tmarhguy/cpu/schematics/ltspice/models/README.md

# SPICE Models

This directory contains SPICE transistor models and libraries used for circuit simulation.

## Model Files

- `mosfet_models.lib` - MOSFET model library

## Usage

Include model files in your SPICE netlists using `.lib` directives:

```
.lib mosfet_models.lib
```
