tmarhguy/cpu/media/design/electric/design_electric_and.png

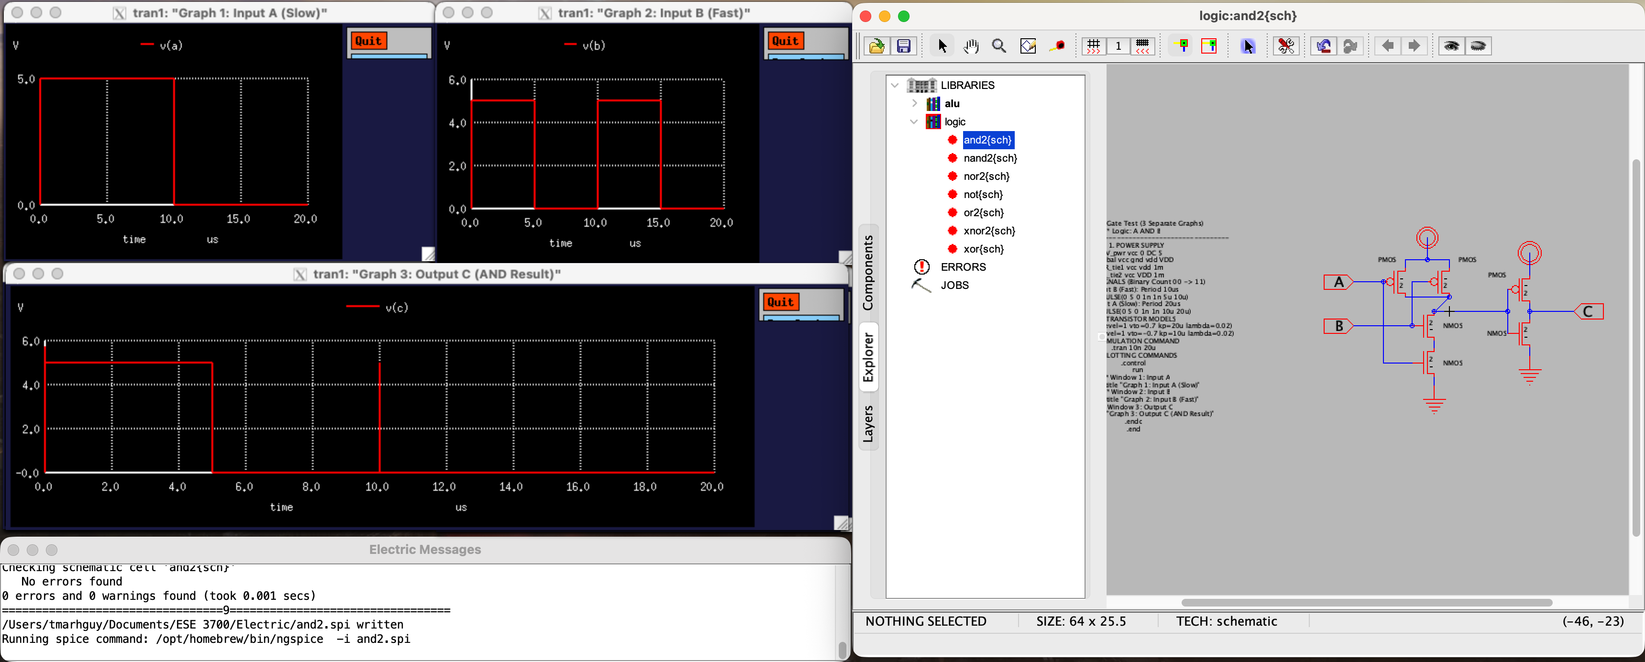
media/design/electric/design_electric_and.png
