tmarhguy/cpu/media/design/electric/design_electric_or.png

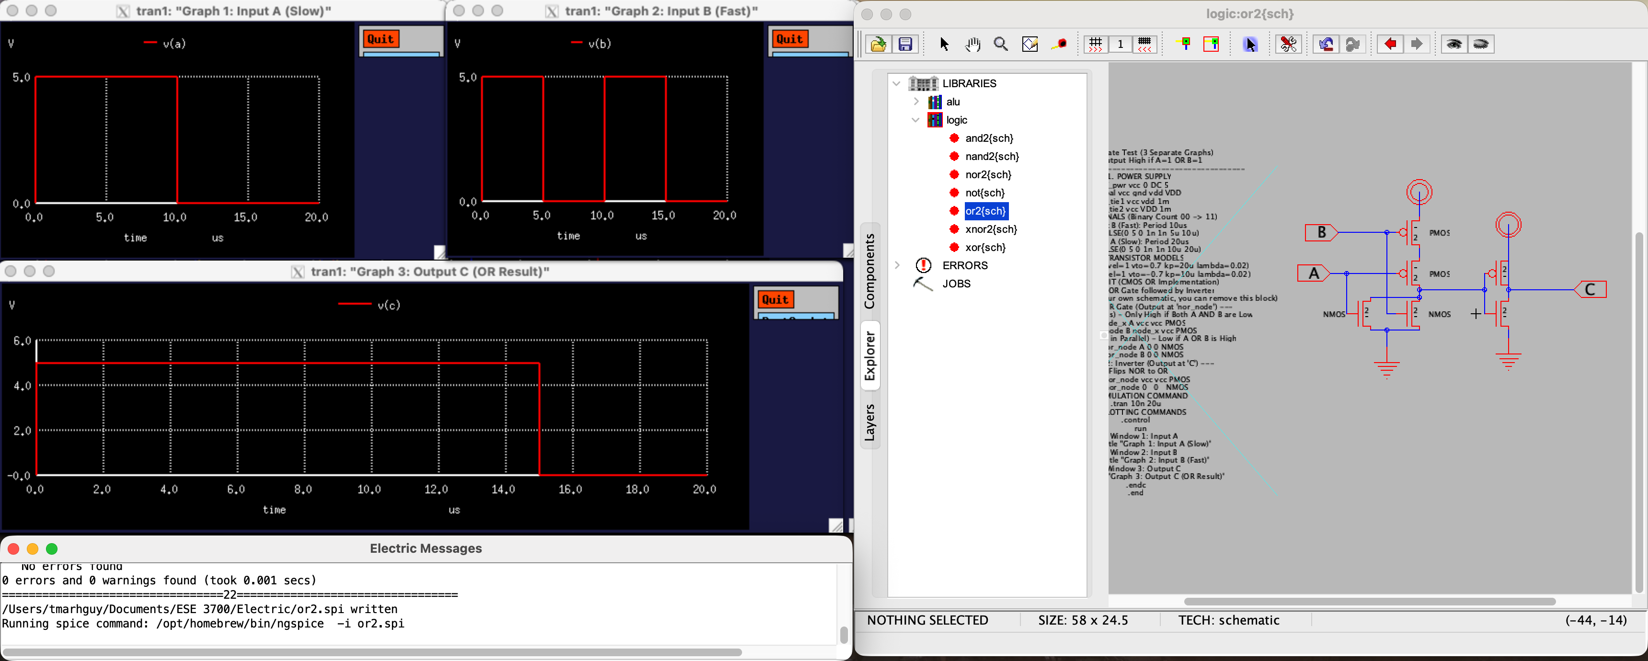
media/design/electric/design_electric_or.png
