tmarhguy/cpu/media/design/electric/design_electric_xnor.png

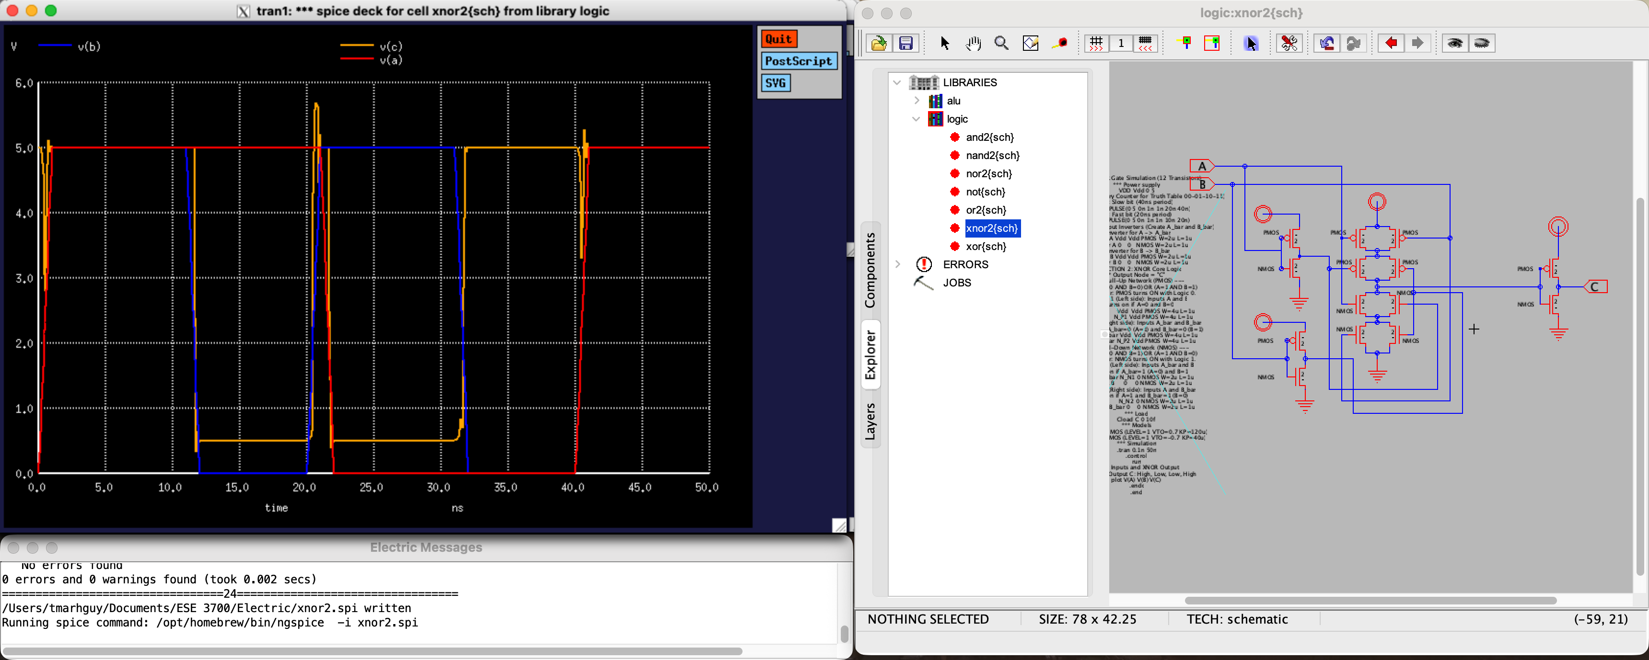
media/design/electric/design_electric_xnor.png
