tmarhguy/cpu/media/design/kicad/design_kicad_control_schematic.jpg

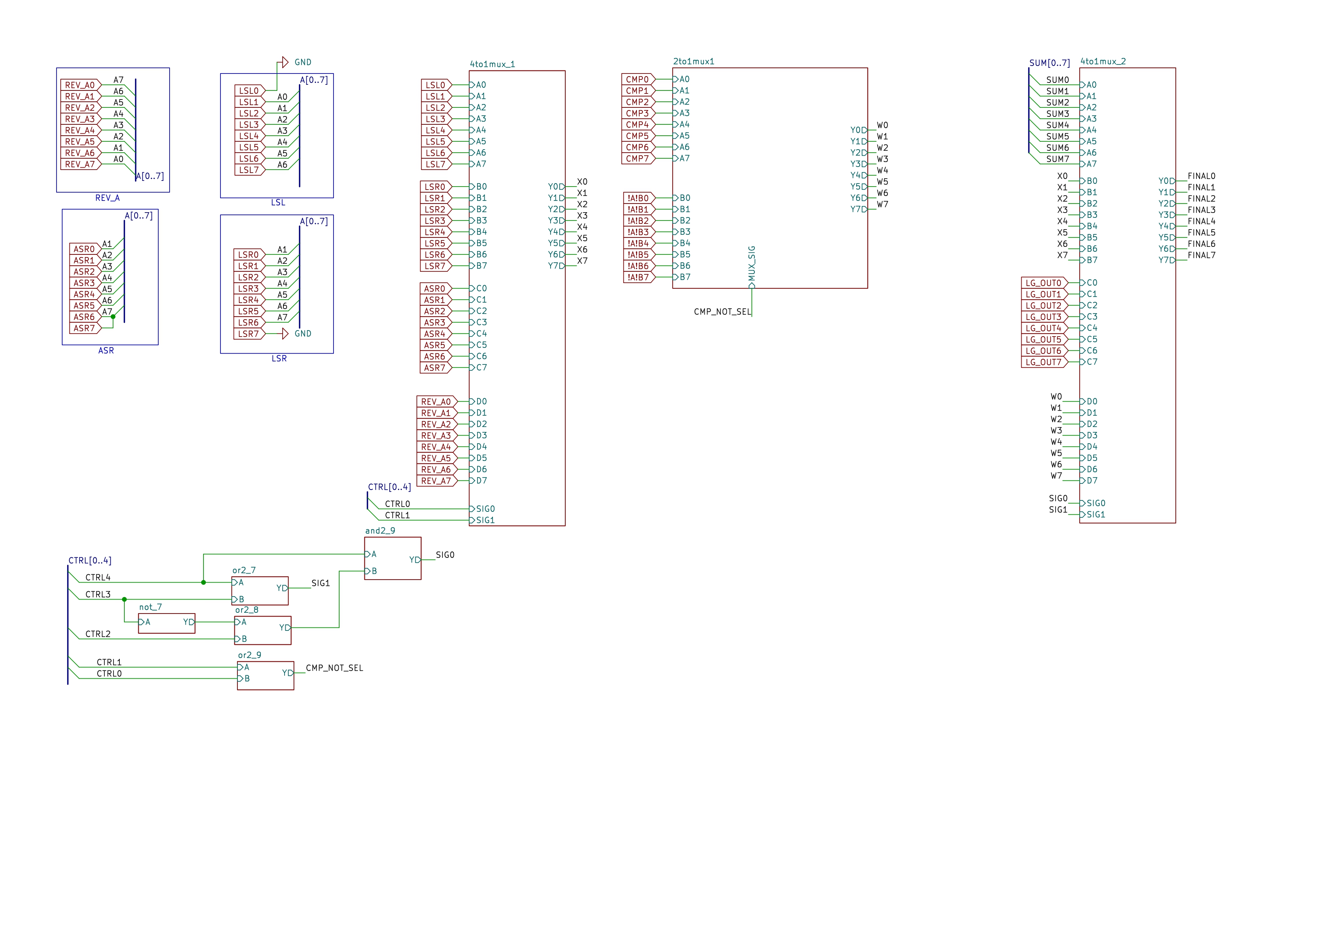
media/design/kicad/design_kicad_control_schematic.jpg
