tmarhguy/cpu/media/design/kicad/design_kicad_flags_schematic.jpg

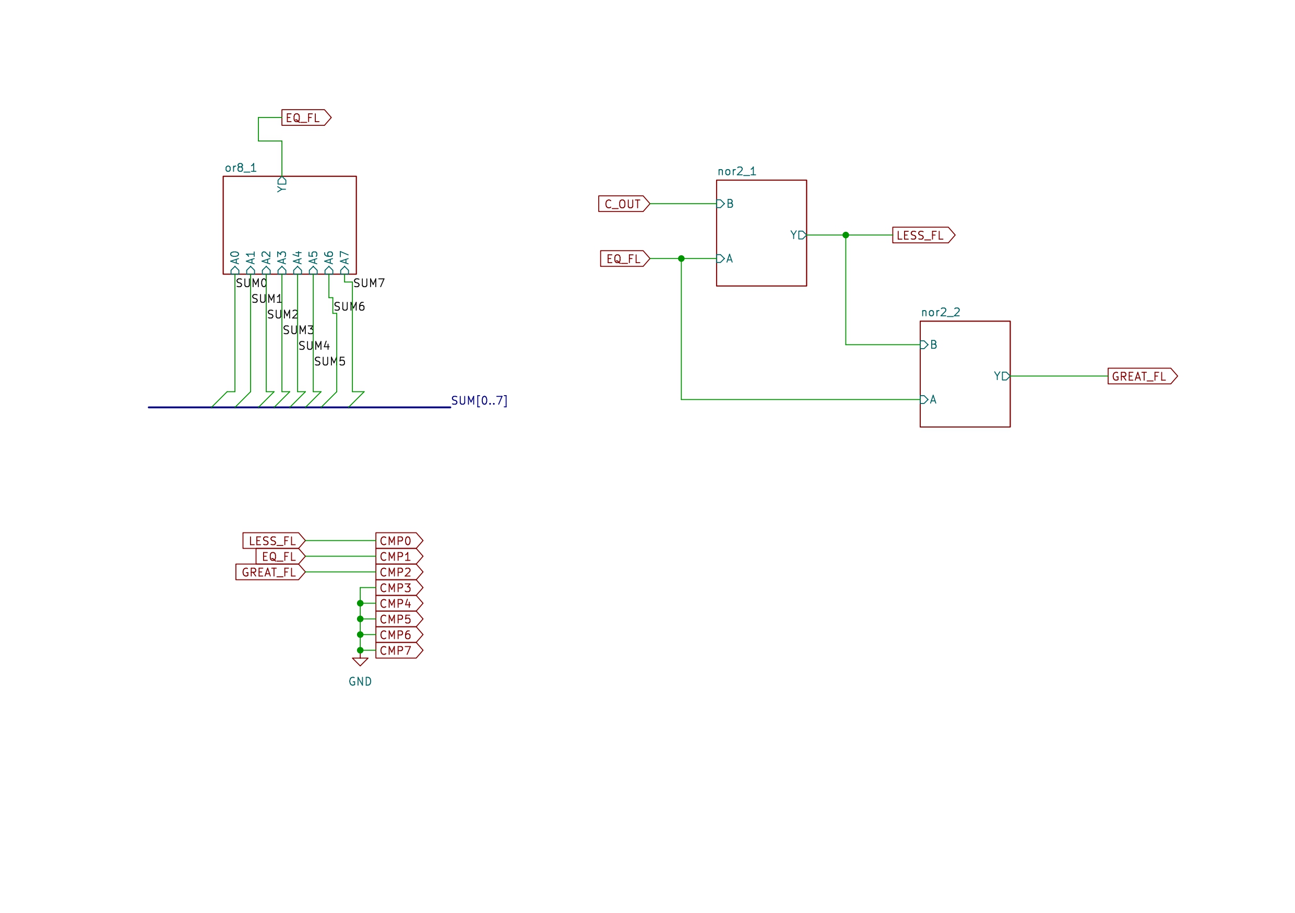
media/design/kicad/design_kicad_flags_schematic.jpg
