tmarhguy/cpu/media/gates/and/and.png

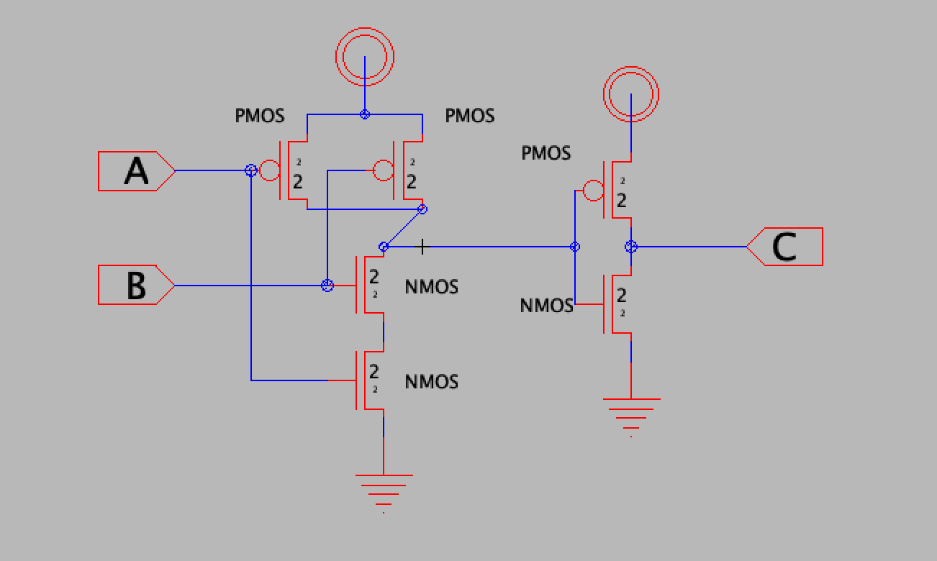
media/gates/and/and.png
