tmarhguy/cpu/media/gates/nand/nand.png

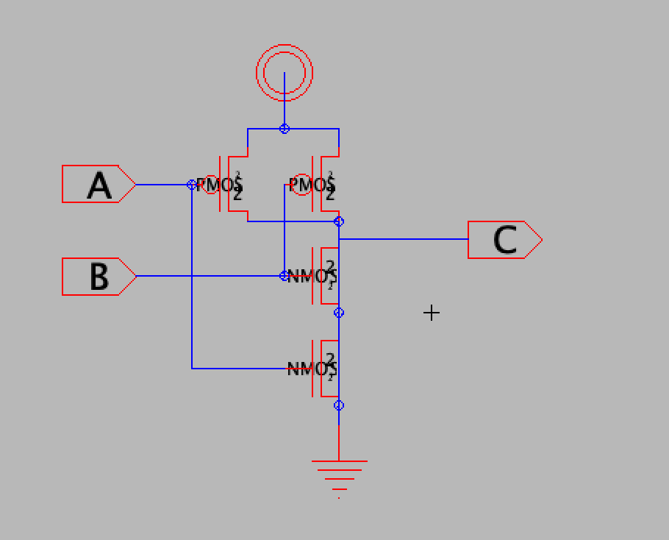
media/gates/nand/nand.png
