tmarhguy/cpu/media/gates/nor/nor.png

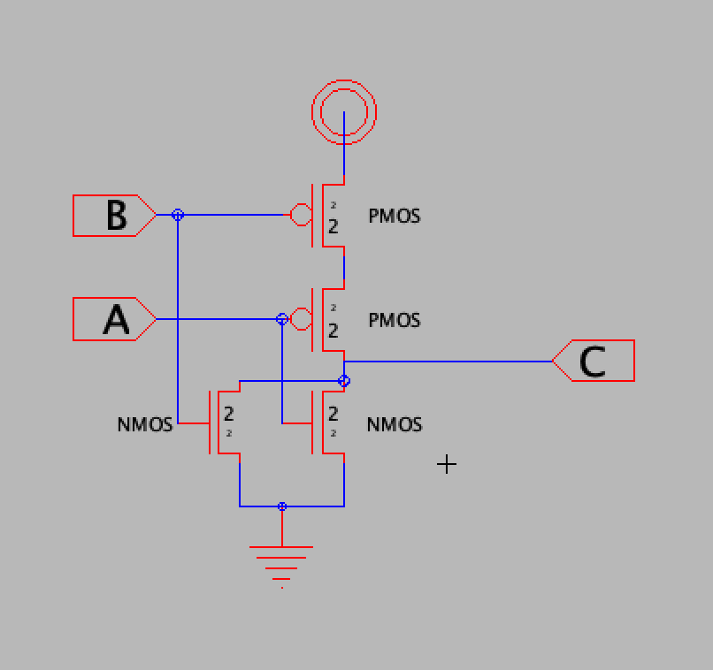
media/gates/nor/nor.png
