tmarhguy/cpu/media/gates/not/not-pcb view.png

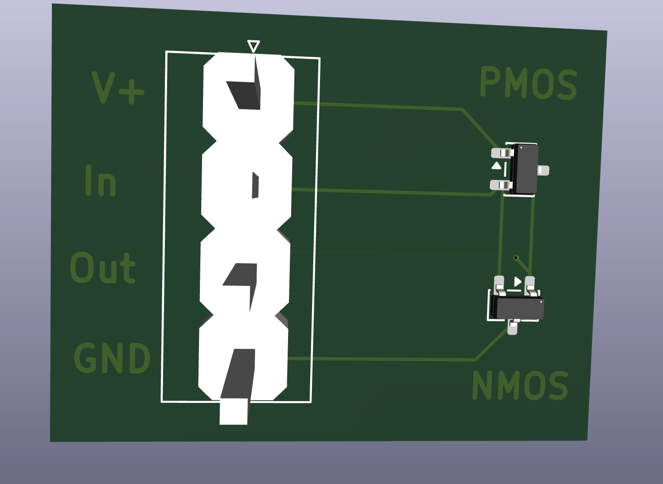
media/gates/not/not-pcb view.png
