tmarhguy/cpu/media/gates/not/not-schematics.png

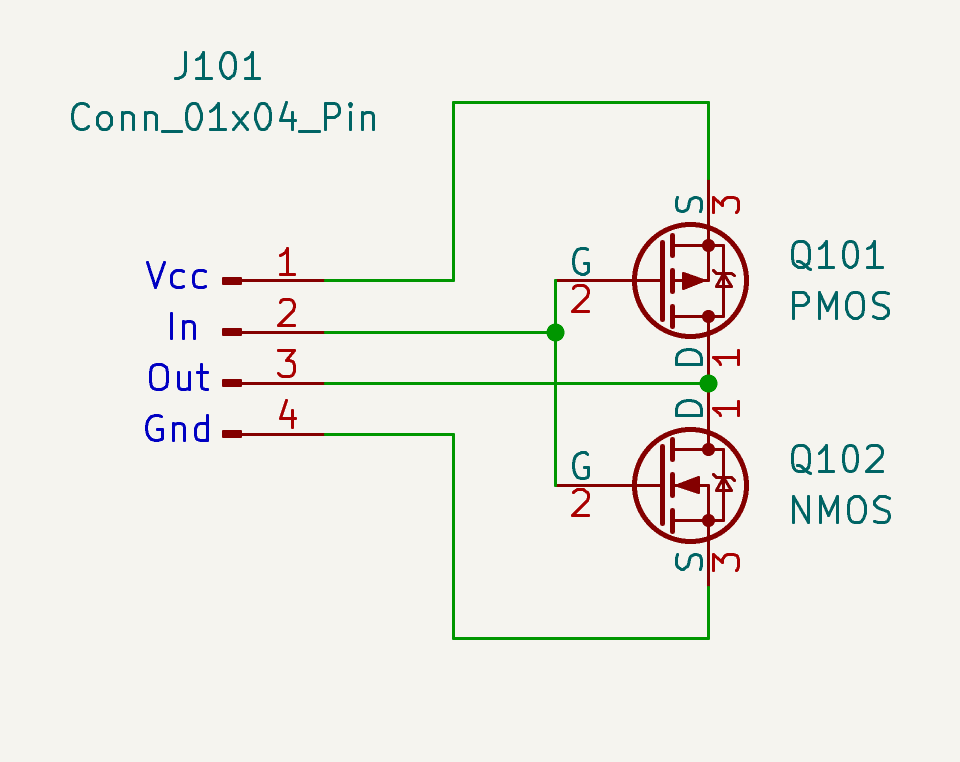
media/gates/not/not-schematics.png
