tmarhguy/cpu/media/gates/not/not.png

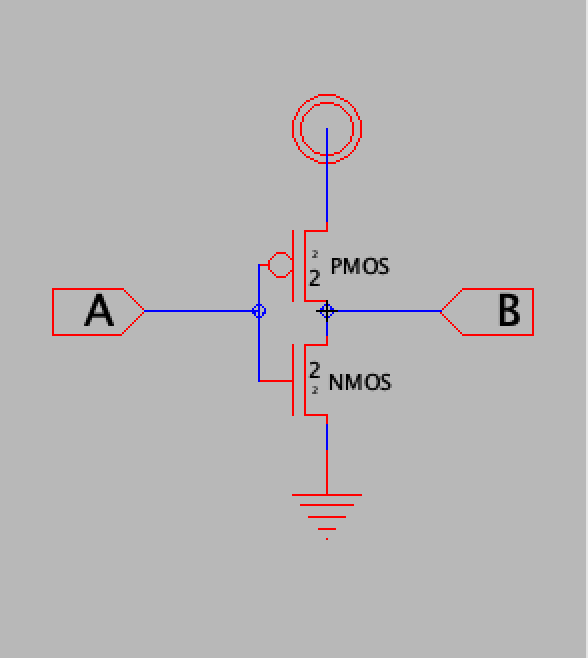
media/gates/not/not.png
