tmarhguy/cpu/media/gates/or/or.png

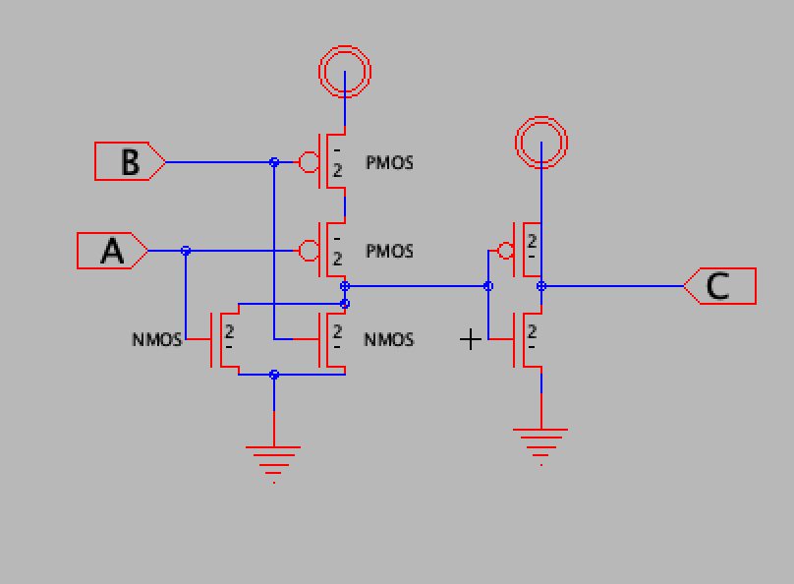
media/gates/or/or.png
