tmarhguy/cpu/media/gates/xnor/xnor.png

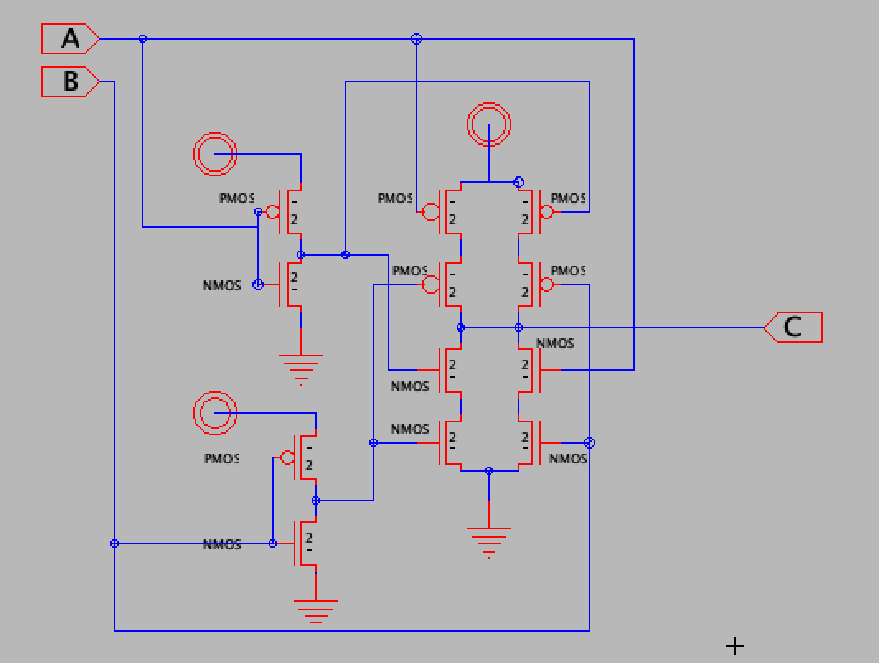
media/gates/xnor/xnor.png
