tmarhguy/cpu/media/gates/xor/xor.png

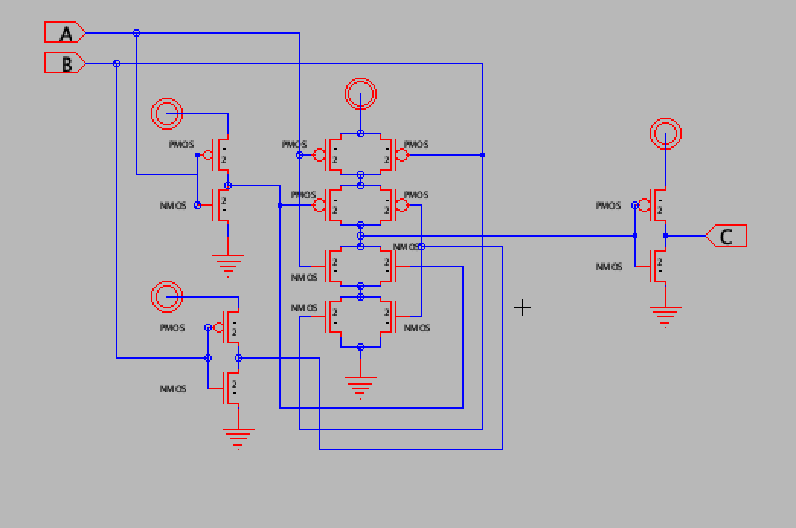
media/gates/xor/xor.png
