tmarhguy/cpu/media/misc/blender-try-2.png

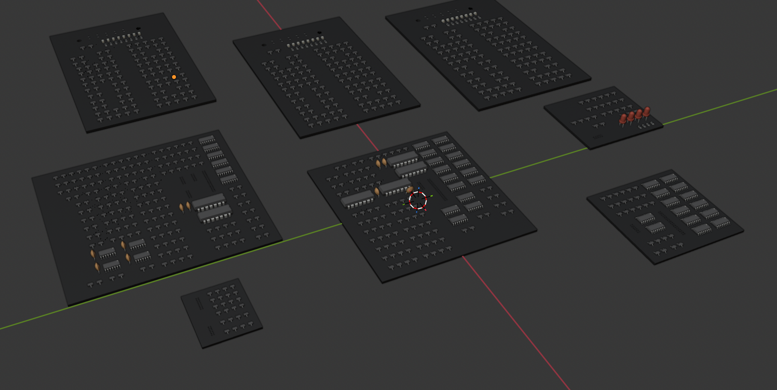
media/misc/blender-try-2.png
