tmarhguy/cpu/media/misc/blender-try.png

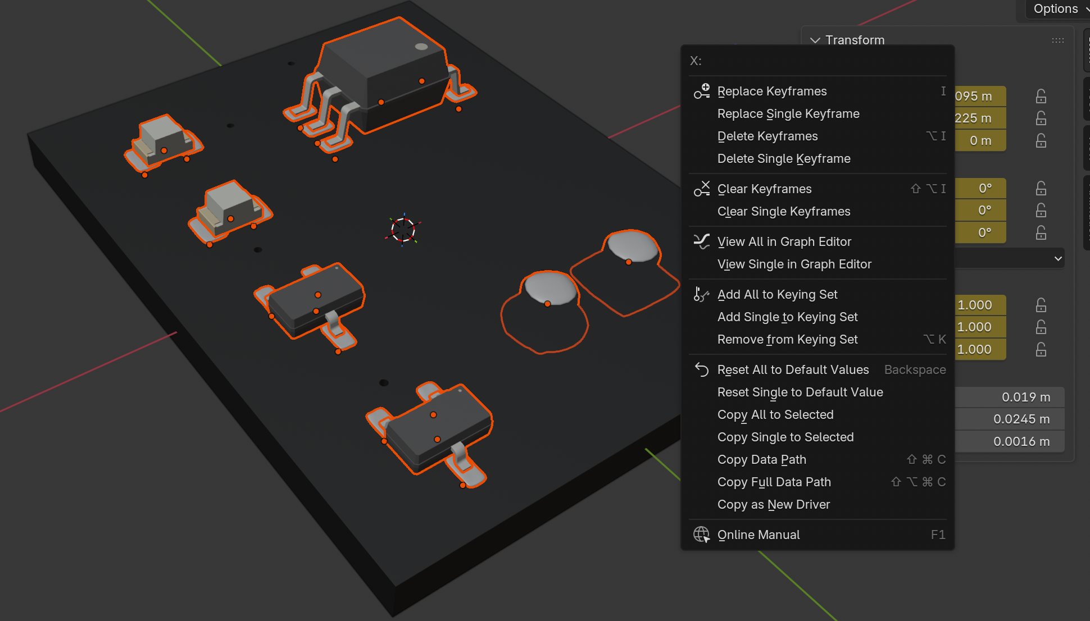
media/misc/blender-try.png
