tmarhguy/cpu/media/pcb/layouts/adder2.png

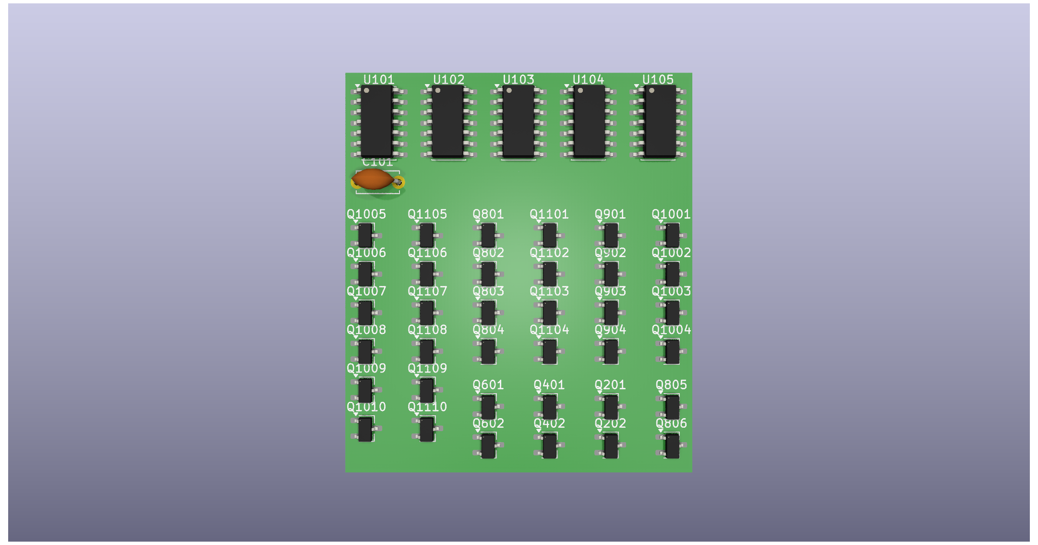
media/pcb/layouts/adder2.png
