tmarhguy/cpu/media/pcb/layouts/adder8.png

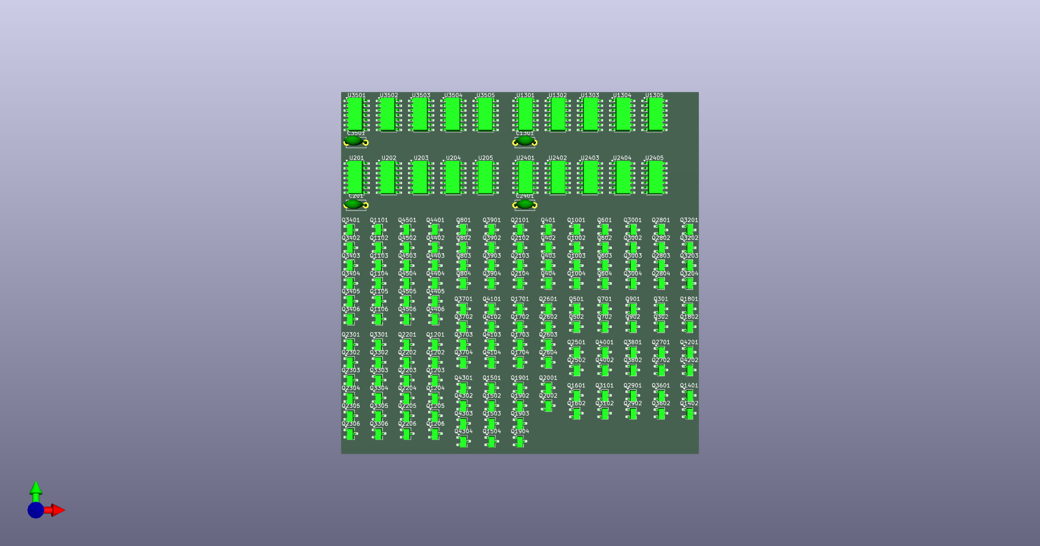
media/pcb/layouts/adder8.png
