tmarhguy/cpu/media/pcb/layouts/led_panel_4.png

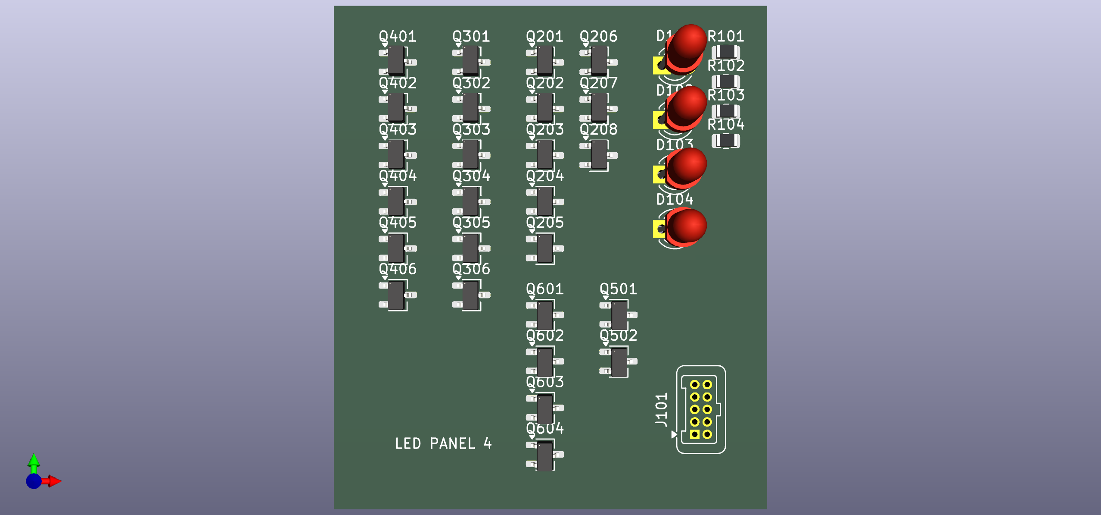
media/pcb/layouts/led_panel_4.png
