tmarhguy/cpu/media/pcb/layouts/pcb_mux_4to1.png

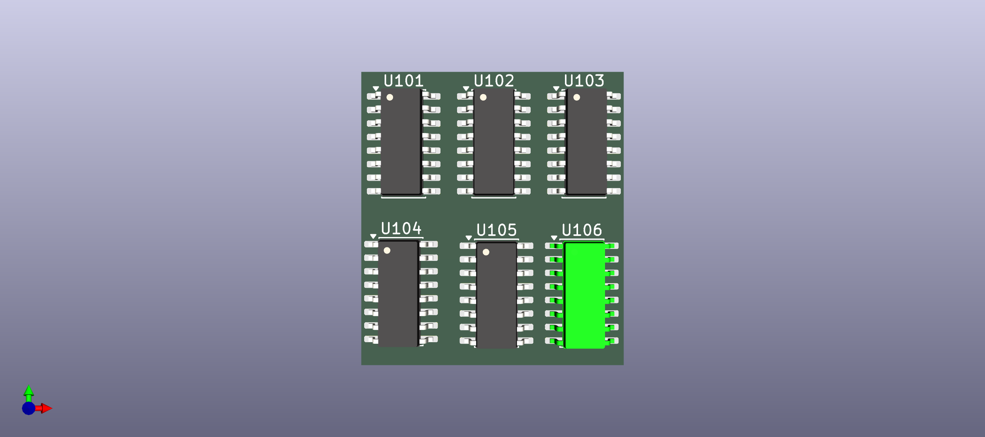
media/pcb/layouts/pcb_mux_4to1.png
