tmarhguy/cpu/media/pcb/layouts/pcb_mux_8to1.png

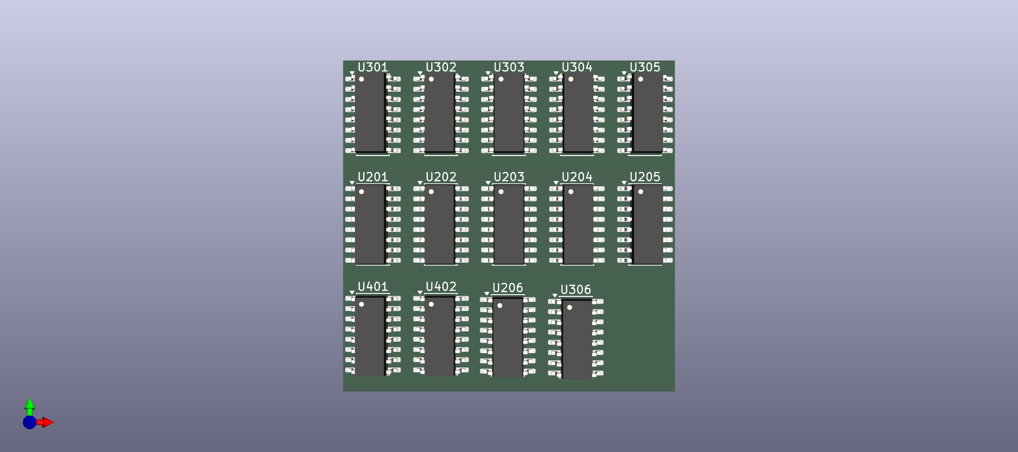
media/pcb/layouts/pcb_mux_8to1.png
