tmarhguy/cpu/media/pcb/renders/not-routed-pcb.png

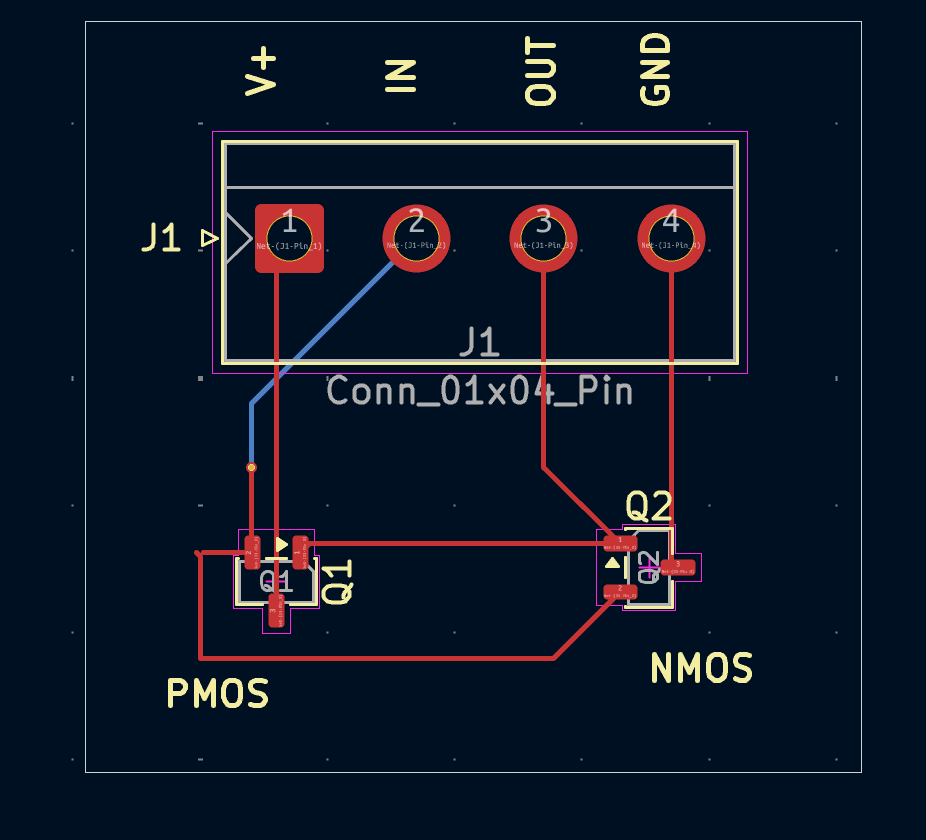
media/pcb/renders/not-routed-pcb.png
