tmarhguy/cpu/media/pcb/renders/unrouted-pcb-ratnet-full-alu.png

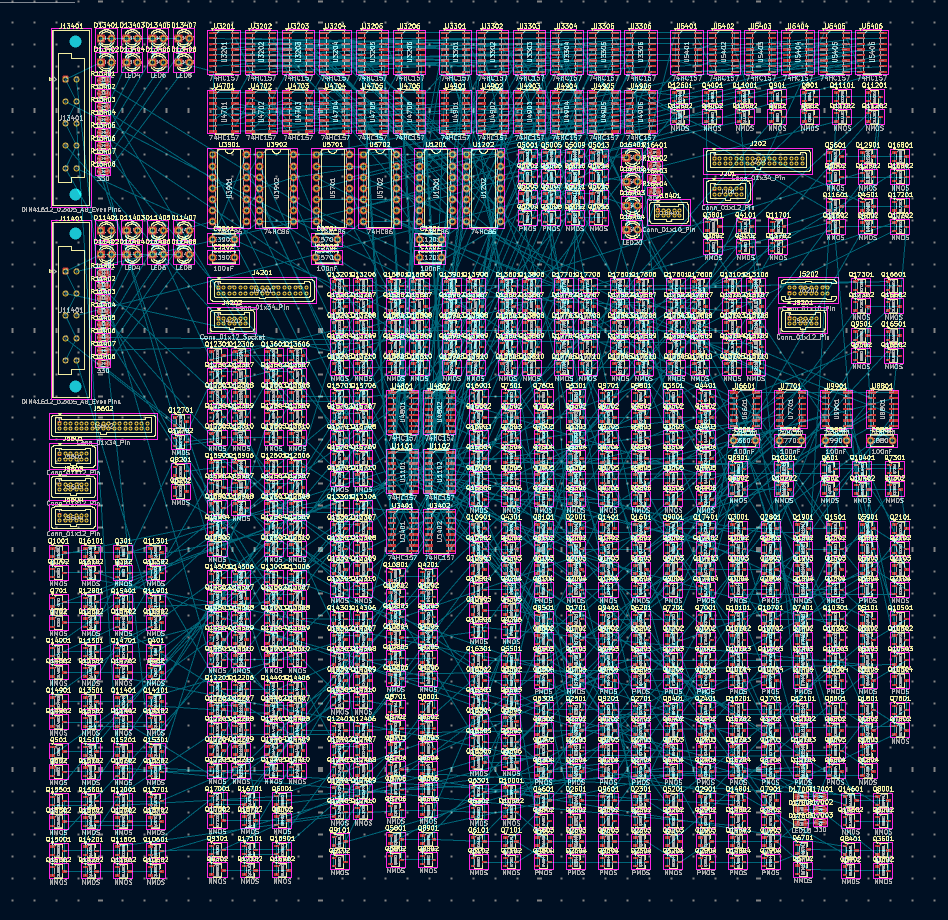
media/pcb/renders/unrouted-pcb-ratnet-full-alu.png
