tmarhguy/cpu/media/photos/hardware/begining-routing-kicad-screenrecord-Cover.jpg

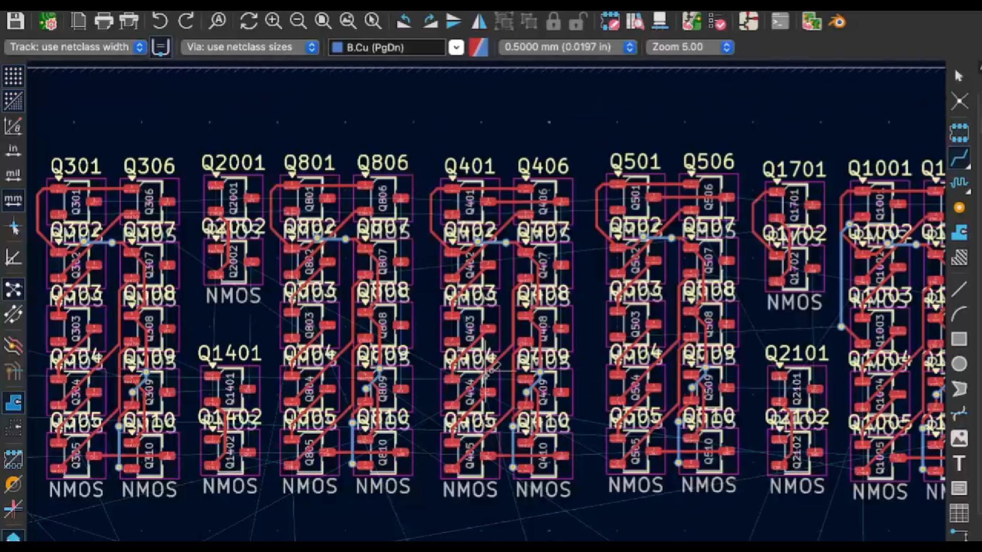
media/photos/hardware/begining-routing-kicad-screenrecord-Cover.jpg
