tmarhguy/cpu/media/schematics/boards/led_panel_3_page-0001.jpg

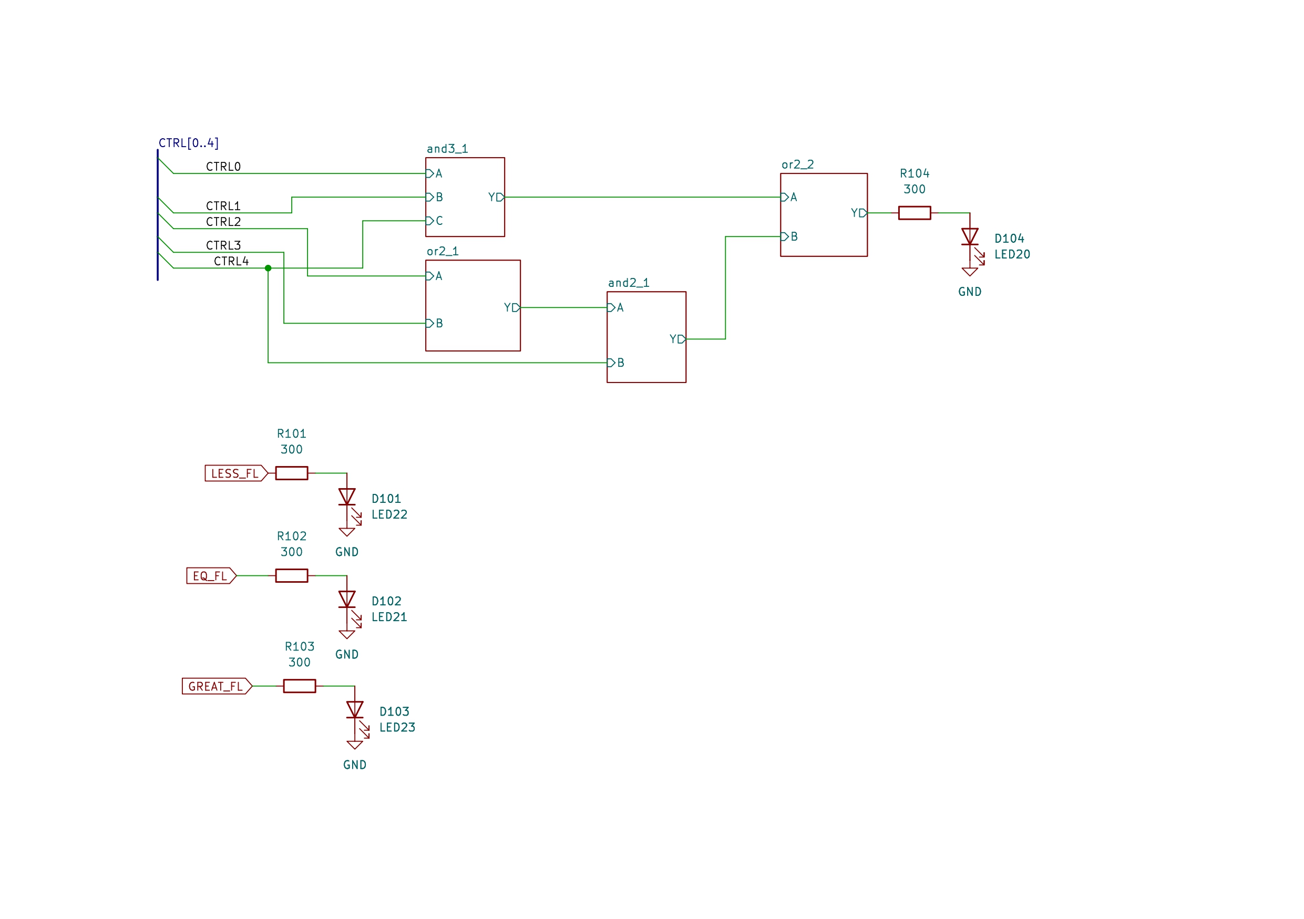
media/schematics/boards/led_panel_3_page-0001.jpg
