tmarhguy/cpu/media/schematics/boards/not_schematics.png

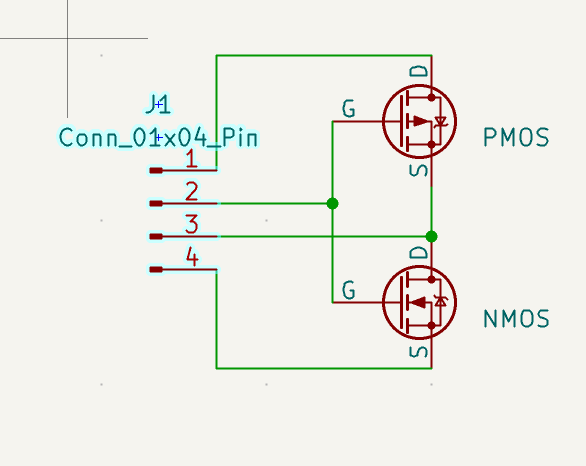
media/schematics/boards/not_schematics.png
