tmarhguy/cpu/media/schematics/gates/adder2_page-0001.jpg

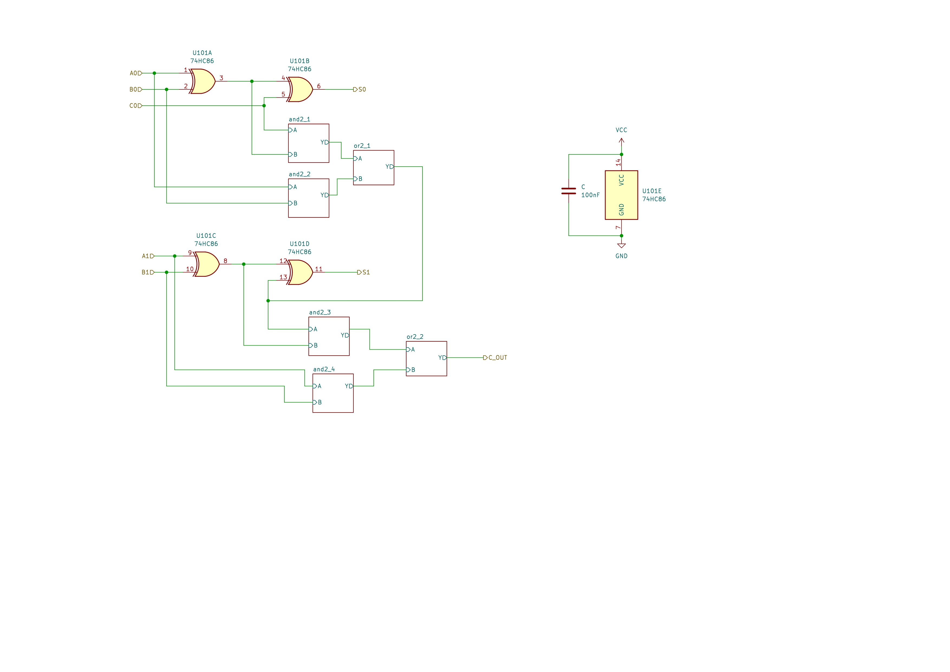
media/schematics/gates/adder2_page-0001.jpg
