tmarhguy/cpu/media/schematics/gates/gate_and_2in_8bit_page-0001.jpg

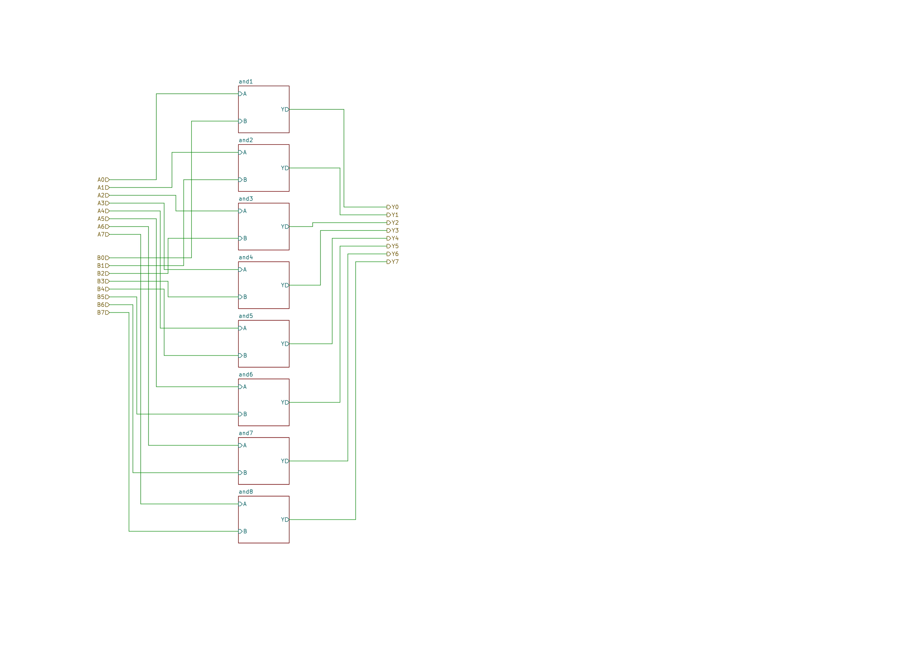
media/schematics/gates/gate_and_2in_8bit_page-0001.jpg
