tmarhguy/cpu/media/schematics/gates/gate_and_3in_page-0001.jpg

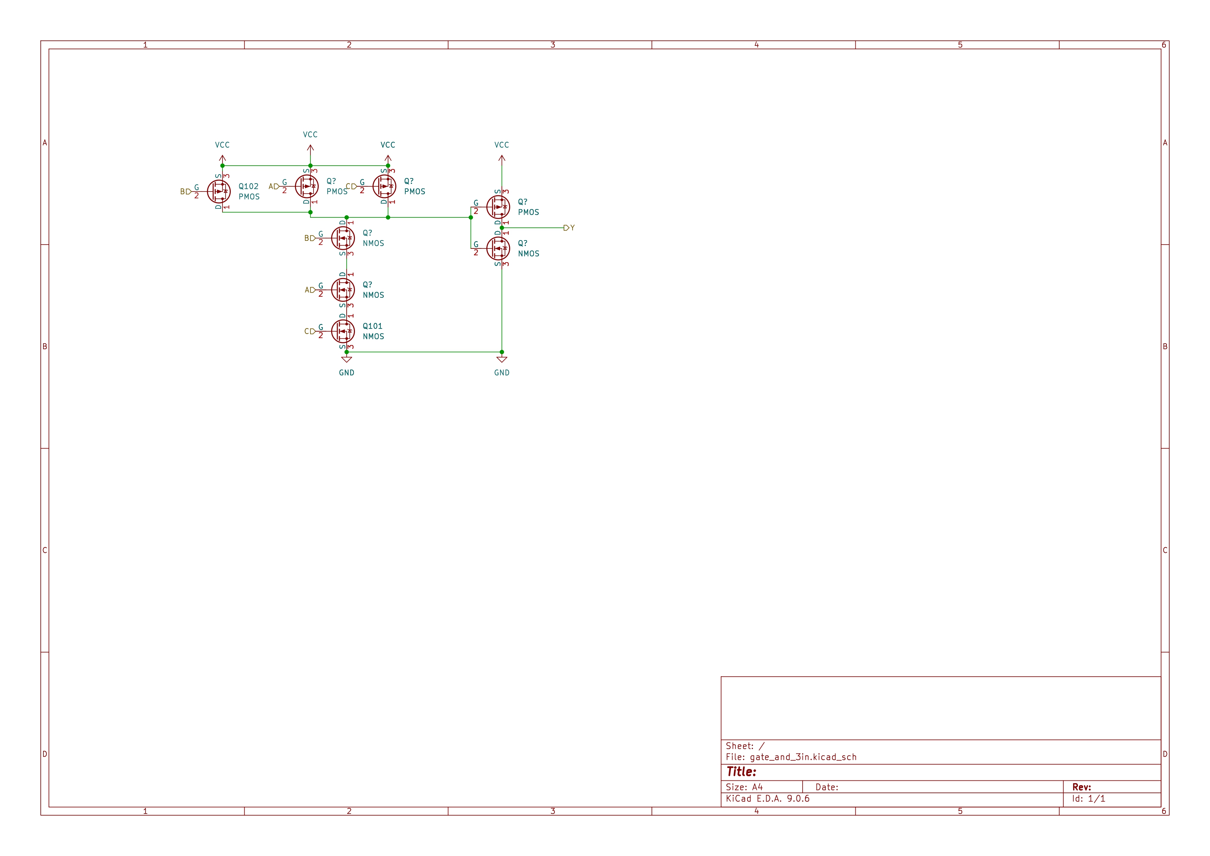
media/schematics/gates/gate_and_3in_page-0001.jpg
