tmarhguy/cpu/media/schematics/gates/gate_and_4in_page-0001.jpg

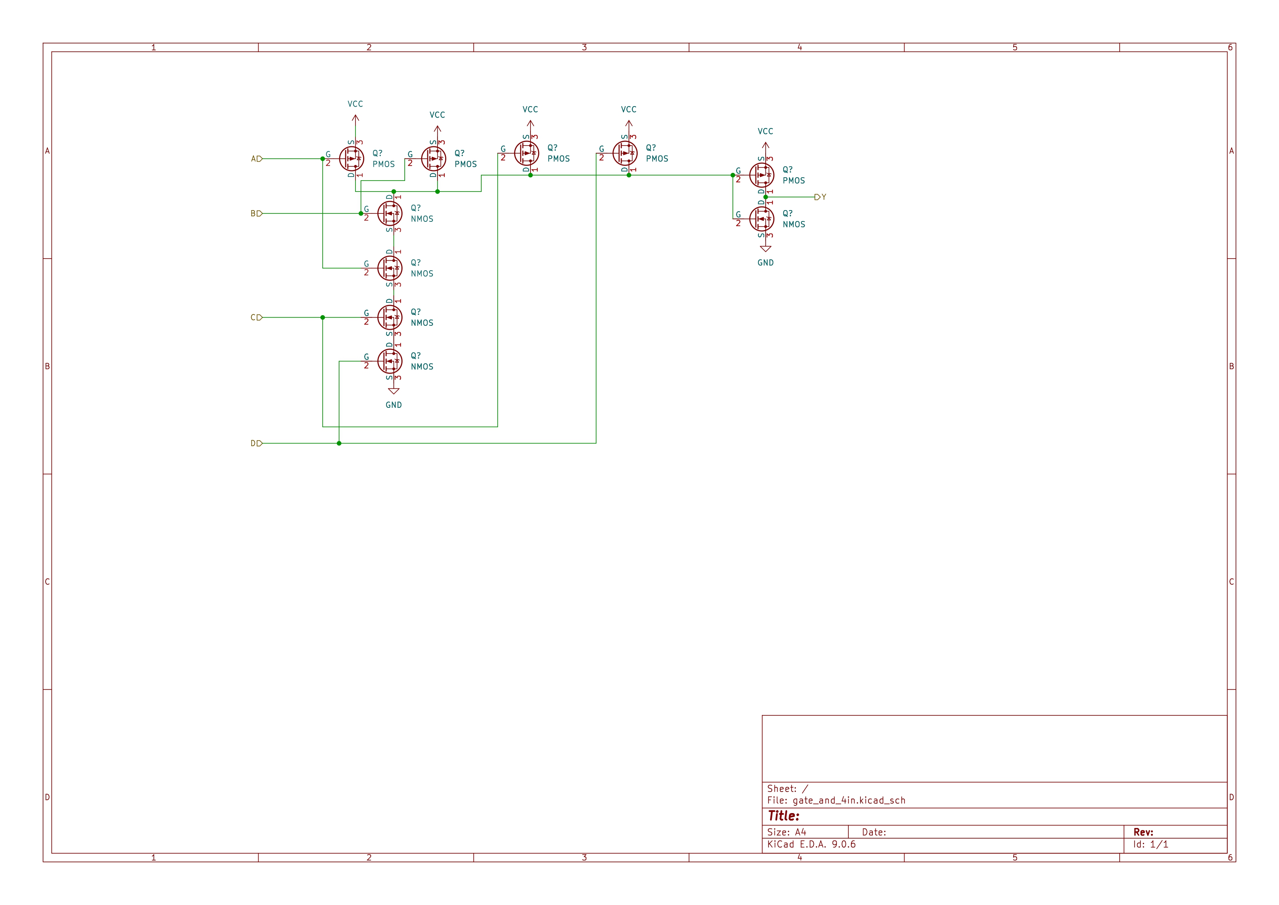
media/schematics/gates/gate_and_4in_page-0001.jpg
