tmarhguy/cpu/media/schematics/gates/gate_nand_2in_8bit_page-0001.jpg

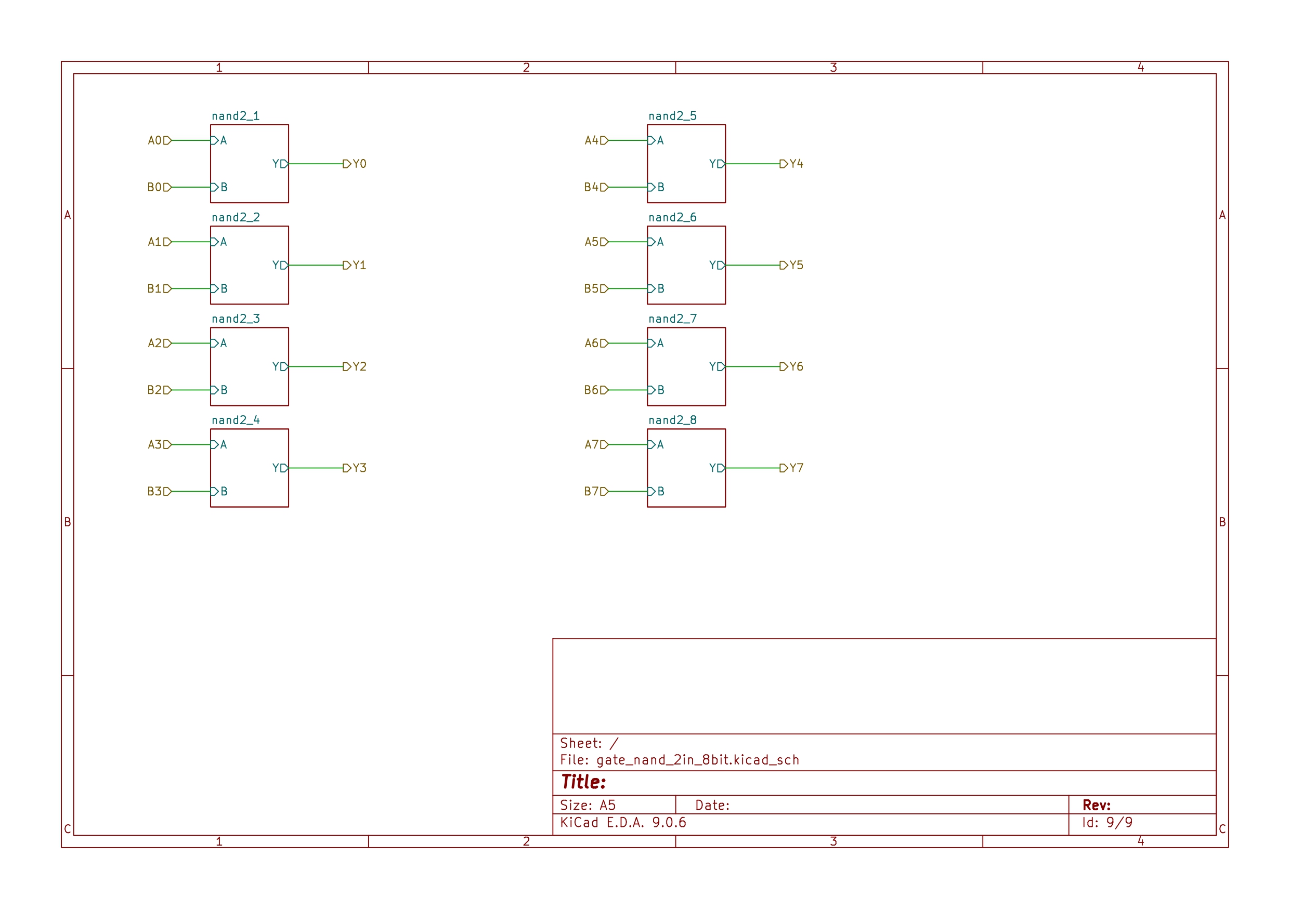
media/schematics/gates/gate_nand_2in_8bit_page-0001.jpg
