tmarhguy/cpu/media/schematics/gates/gate_nor_8in_1bit_page-0001.jpg

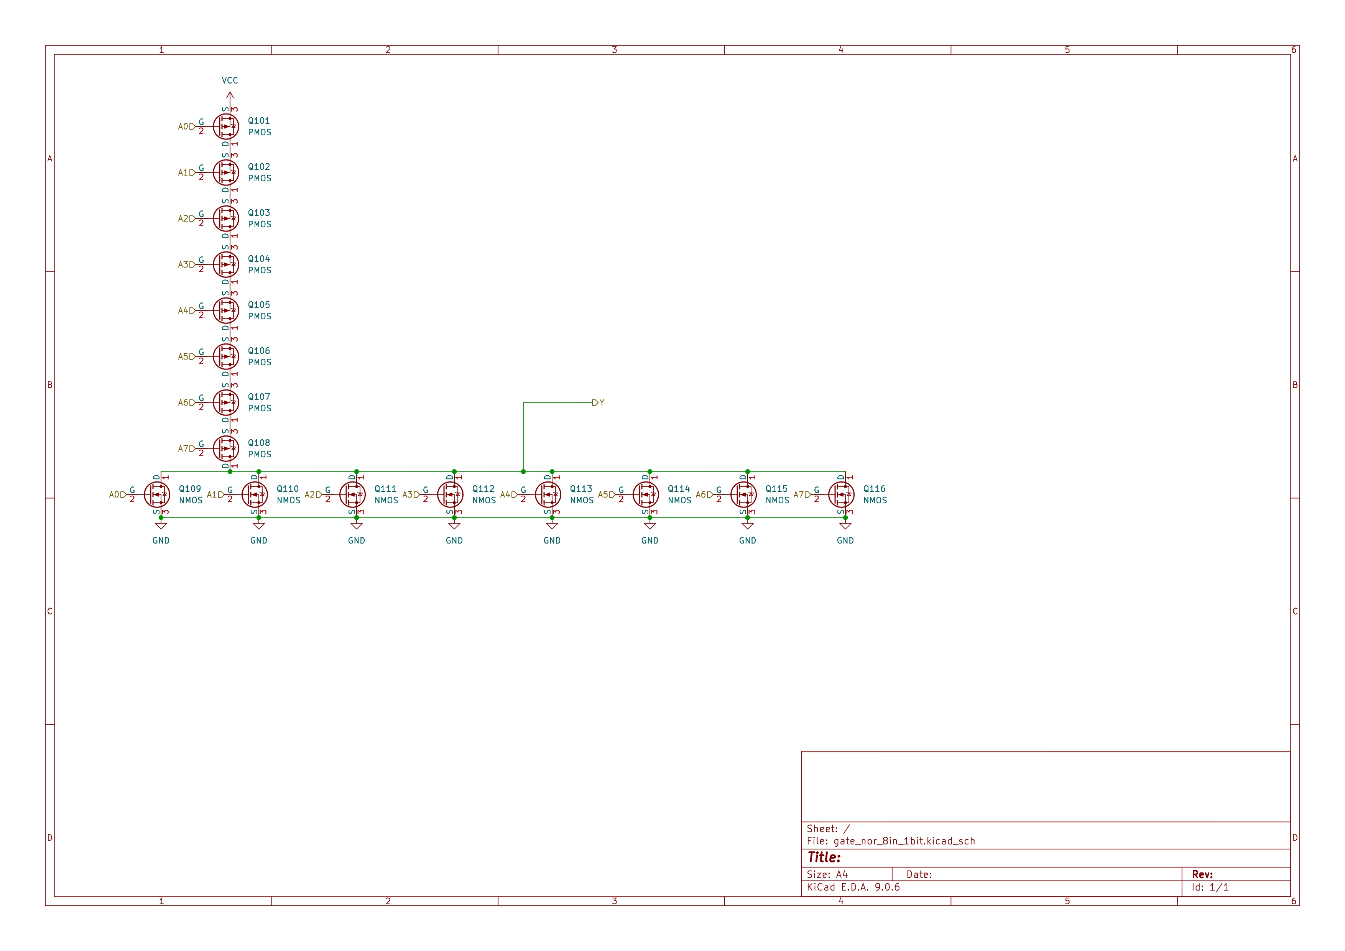
media/schematics/gates/gate_nor_8in_1bit_page-0001.jpg
