tmarhguy/cpu/media/schematics/gates/gate_xnor_2in_page-0001.jpg

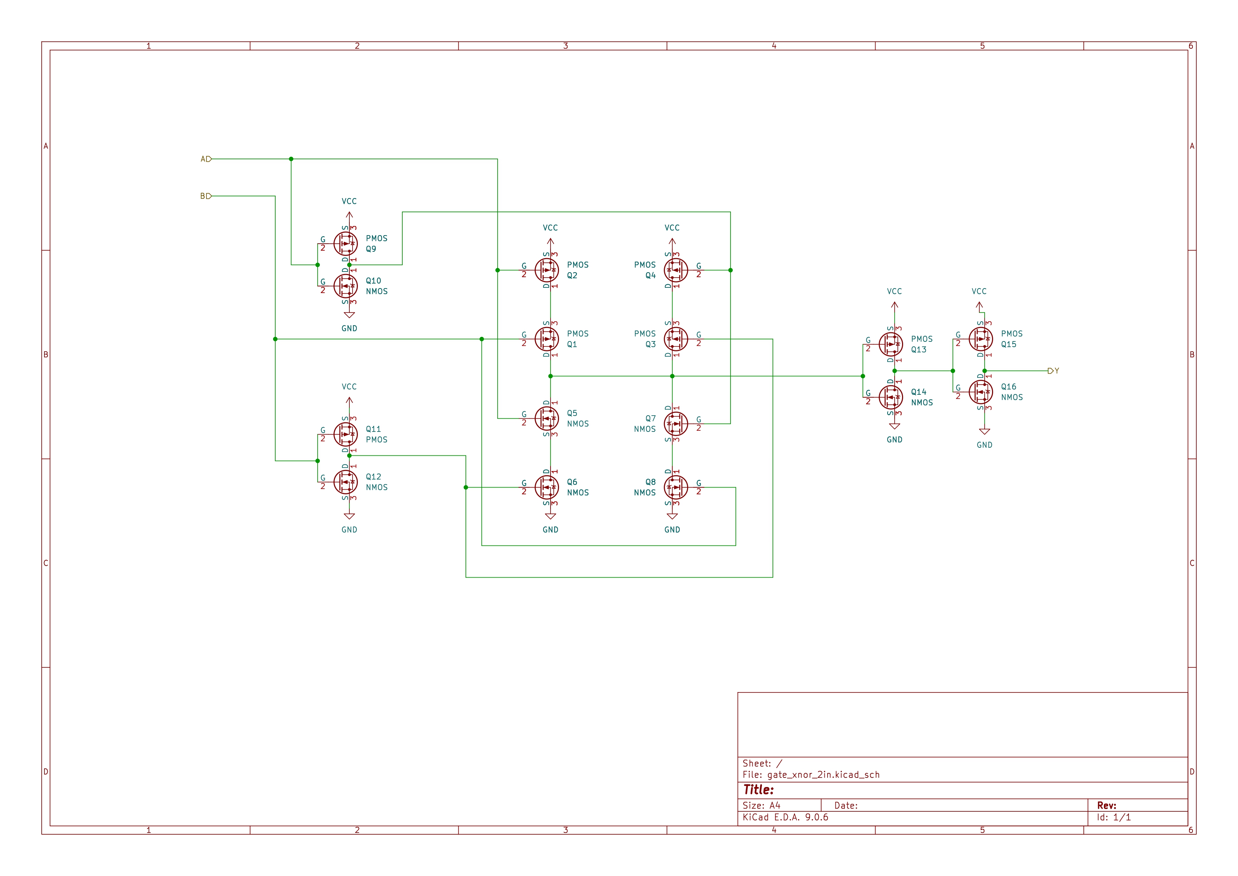
media/schematics/gates/gate_xnor_2in_page-0001.jpg
