tmarhguy/cpu/media/schematics/gates/gate_xor_8bit_page-0001.jpg

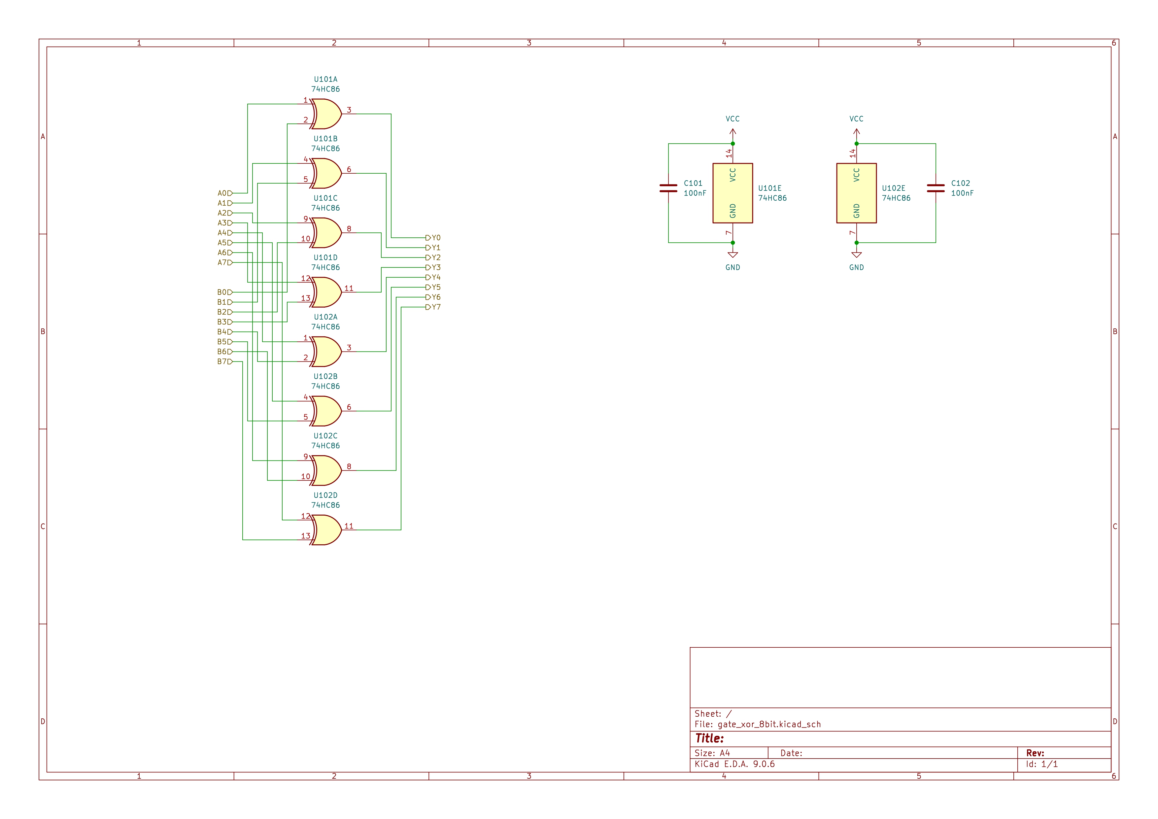
media/schematics/gates/gate_xor_8bit_page-0001.jpg
