tmarhguy/cpu/media/schematics/gates/mux_8to1_8bit_page-0001.jpg

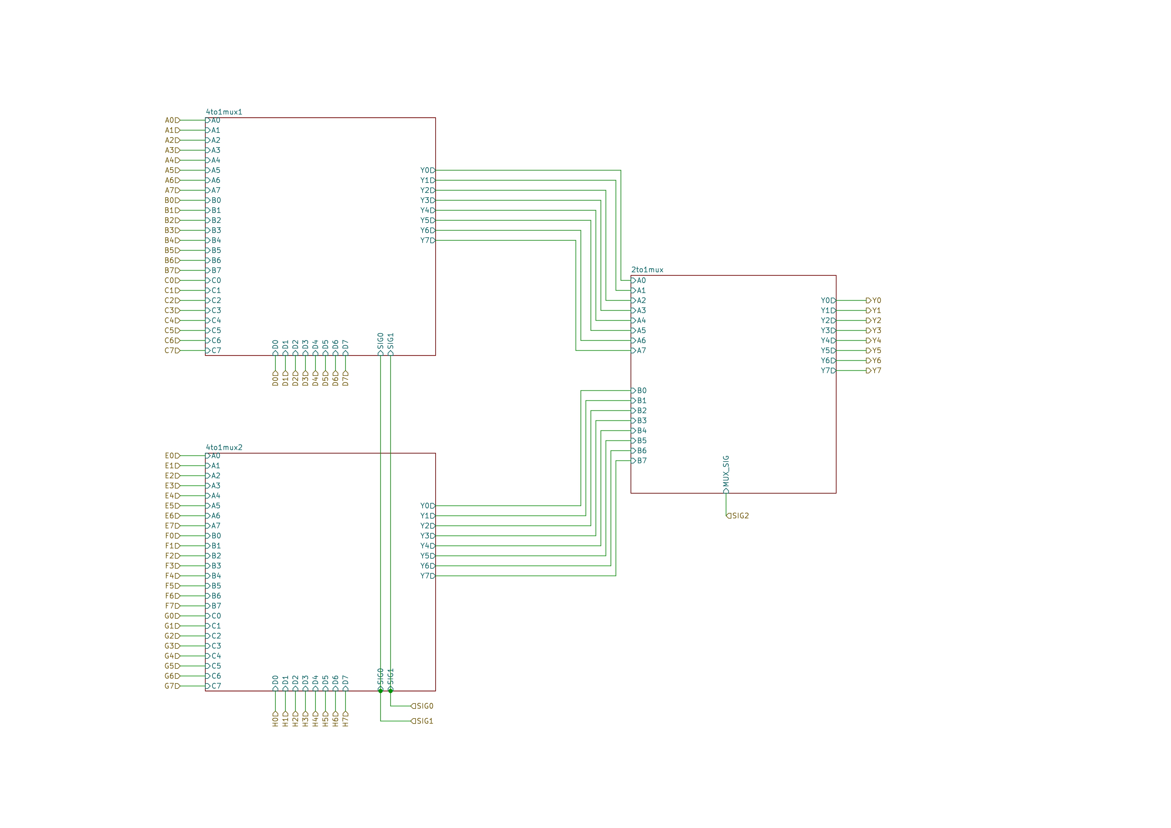
media/schematics/gates/mux_8to1_8bit_page-0001.jpg
