tmarhguy/cpu/media/simulations/spice/input-spice-a-transient-anal.png

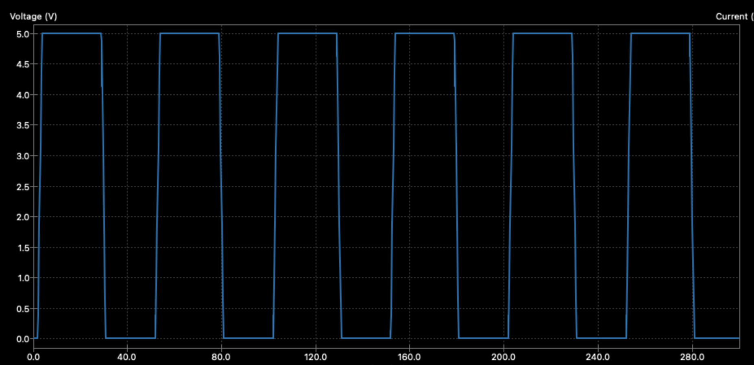
media/simulations/spice/input-spice-a-transient-anal.png
