tmarhguy/cpu/media/simulations/spice/input-spice-b-transient-anal.png

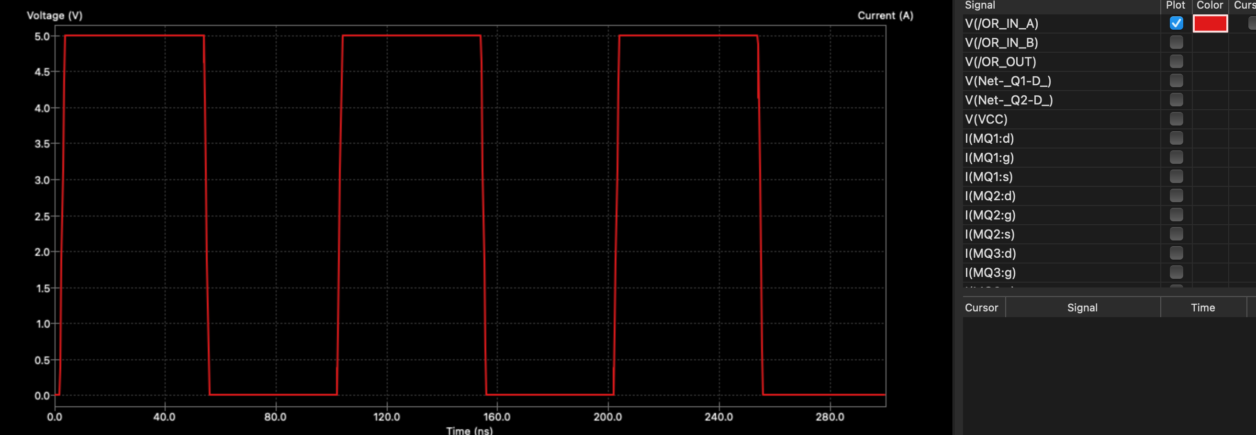
media/simulations/spice/input-spice-b-transient-anal.png
