tmarhguy/cpu/media/simulations/spice/not-spice.png

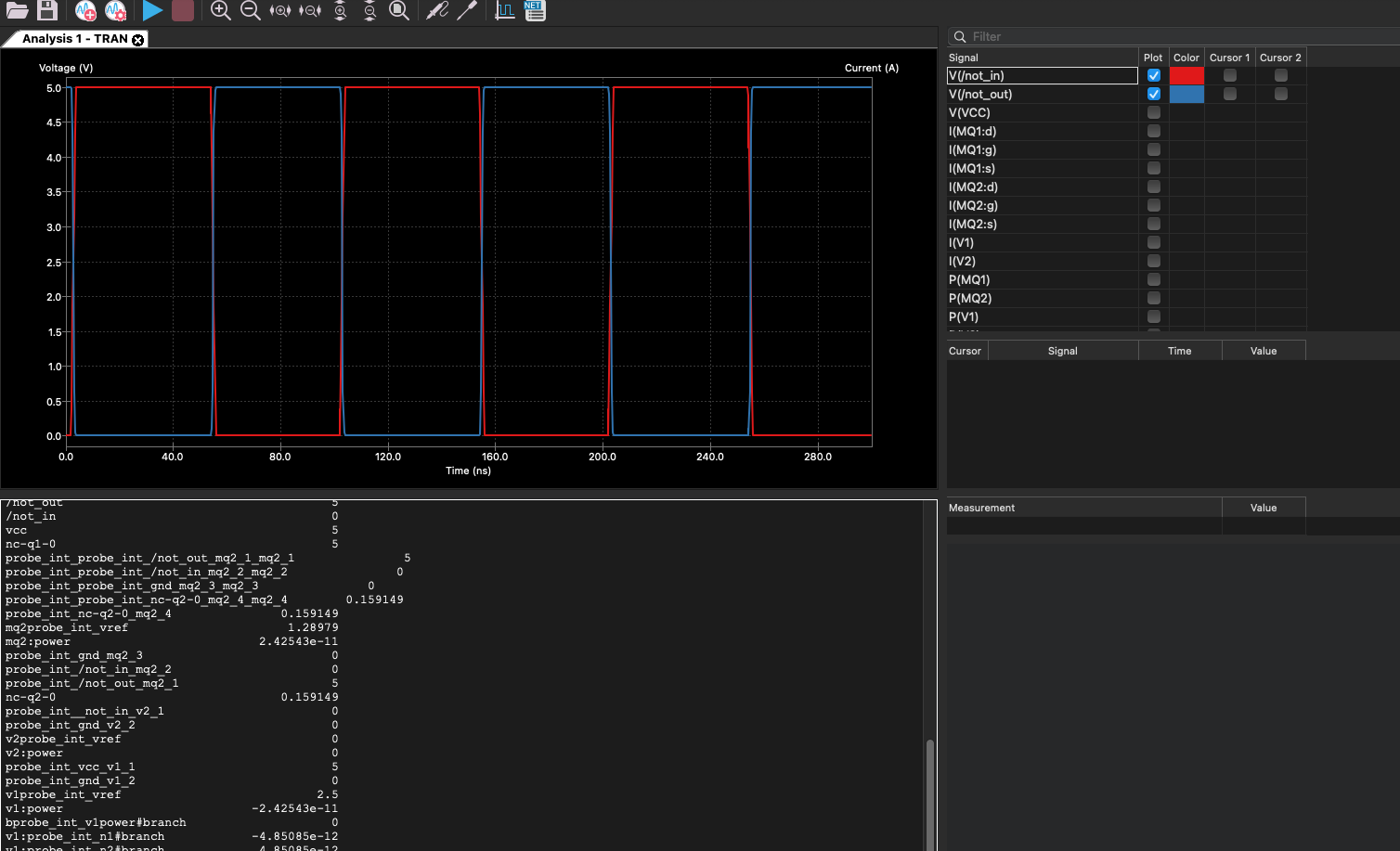
media/simulations/spice/not-spice.png
