tmarhguy/cpu/media/simulations/spice/spice-wrong-used-wrong-mosfet-sim-module.png

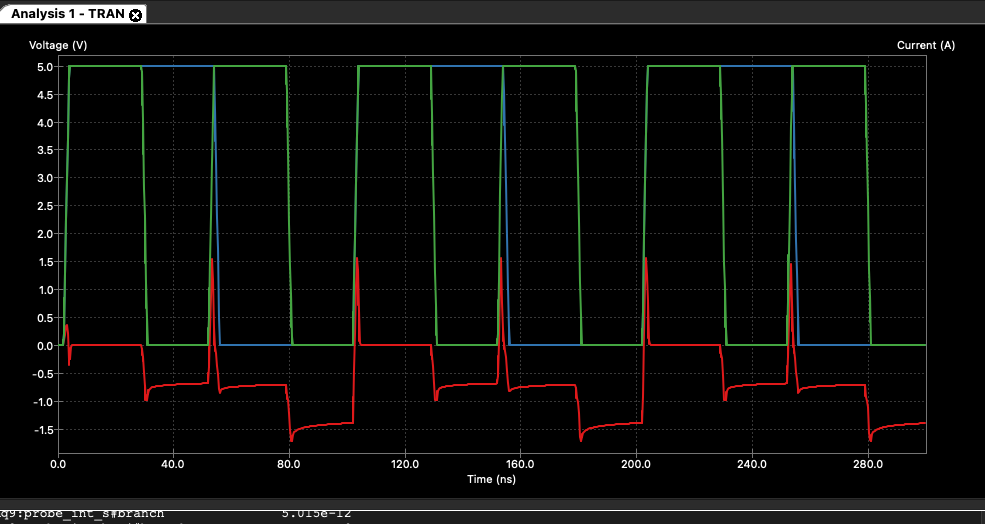
media/simulations/spice/spice-wrong-used-wrong-mosfet-sim-module.png
