tmarhguy/cpu/media/gates/not/not-pcb-order-jlcpcb.png

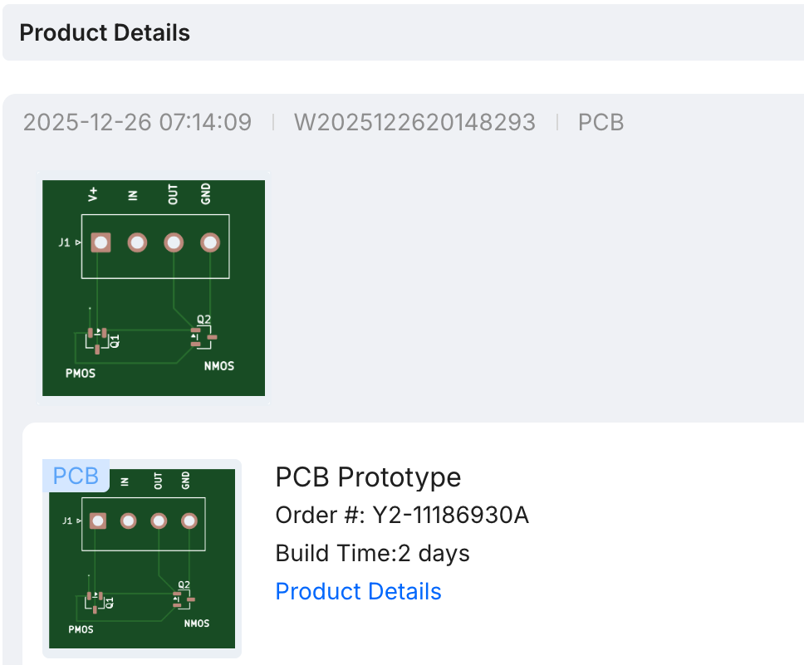
media/gates/not/not-pcb-order-jlcpcb.png
