tmarhguy/cpu/test/INDUSTRY_STANDARD_TESTING.md

# Industry-Standard Testing Approaches for Hardware

> Comparison of testing methodologies used in hardware verification

This document compares different testing approaches used in industry and academia for hardware verification.

---

## Current Implementation

**Python Test Suite** (Current)
- Good for: Functional verification, algorithm validation
- Used by: Software teams, research labs
- Pros: Fast development, easy to read, great for CI/CD
- Cons: Not cycle-accurate, doesn't test actual hardware

## Industry-Standard Approaches

### 1. SystemVerilog/UVM Testbench

**THE GOLD STANDARD for ASIC/FPGA verification**

- **Used by**: Intel, AMD, NVIDIA, Apple, Qualcomm, ARM
- **Tools**: ModelSim, QuestaSim, VCS, Xcelium
- **Language**: SystemVerilog with UVM (Universal Verification Methodology)
- **Coverage**: Functional, code, assertion coverage

**Why it's best:**
- Direct hardware simulation
- Cycle-accurate timing
- Industry standard for chip verification
- Built-in coverage metrics
- Assertion-based verification

### 2. C++ with Verilator ⭐⭐⭐⭐

**Open-source alternative, very popular**

- **Used by**: Google, Western Digital, SpaceX, startups
- **Tools**: Verilator (compiles Verilog to C++)
- **Speed**: 10-100x faster than traditional simulators
- **Free**: Open source

**Why it's good:**
- Much faster than traditional simulators
- Can integrate with C++ testbenches
- Free and open source
- Used in production at major companies

### 3. Formal Verification

**Mathematical proof of correctness**

- **Used by**: Intel, AMD, ARM (for critical components)
- **Tools**: Cadence JasperGold, Synopsys VC Formal
- **Method**: Proves properties mathematically

**Why it's important:**
- Finds corner cases traditional testing misses
- Provides mathematical proof
- Required for safety-critical systems

### 4. FPGA Hardware Testing

**Testing on actual hardware**

- **Used by**: Everyone doing FPGA development
- **Tools**: Vivado, Quartus, SignalTap
- **Method**: Deploy to FPGA and test

### 5. Python (Current)

**Good for early development**

- **Used by**: Algorithm development, early verification
- **Tools**: pytest, cocotb
- **Speed**: Fast for development

## Recommendation for Your ALU

Based on industry practices, you should have:

### Priority 1: SystemVerilog Testbench (You already have this)

Located in: `sim/FPGA/testbench/alu_tb.v`

**Status:** Complete SystemVerilog testbench exists

### Priority 2: Add C++ with Verilator

**Benefits:**
- Faster simulation (4-5x faster than Python)
- Can load JSON test vectors
- Industry-standard at Google, etc.
- Hardware-level verification

**Status:** C++ testbench exists in `test/cpp/` (see [cpp/README.md](cpp/README.md))

### Priority 3: Keep Python for CI/CD (You have this)

**Benefits:**
- Fast iteration
- Easy to run in GitHub Actions
- Good for regression testing
- No hardware dependencies

**Status:** Complete Python test suite in `test/test_alu.py`

### Priority 4: Add Formal Verification (Optional)
- For critical operations (arithmetic, flags)
- Mathematical proof of correctness

## Implementation Plan

**Current status:**

1. **Python suite** - Complete (1.24M exhaustive tests)
2. **C++ Verilator testbench** - Complete (see `test/cpp/`)
3. **SystemVerilog testbench** - Complete (see `sim/FPGA/testbench/`)
4. **Formal properties** - Future enhancement (optional)

**Recommendation:** Use Python for development and CI/CD, C++ Verilator for final hardware verification.
