tmarhguy/cpu/docs/verification/test-matrix.md

# Test Matrix

Comprehensive test coverage matrix for all ALU operations.

## Operation Coverage

| Operation | Test Vectors | Status |
|---|---|---|
| ADD | [`test/add_sub.json`](../../test/add_sub.json) | Covered |
| SUB | [`test/add_sub.json`](../../test/add_sub.json) | Covered |
| NAND | [`test/logic_ops.json`](../../test/logic_ops.json) | Covered |
| NOR | [`test/logic_ops.json`](../../test/logic_ops.json) | Covered |
| XOR | [`test/logic_ops.json`](../../test/logic_ops.json) | Covered |
| PASS A | [`test/logic_ops.json`](../../test/logic_ops.json) | Covered |
| PASS B | [`test/logic_ops.json`](../../test/logic_ops.json) | Covered |
| AND | [`test/logic_ops.json`](../../test/logic_ops.json) | Covered |
| OR | [`test/logic_ops.json`](../../test/logic_ops.json) | Covered |
| XNOR | [`test/logic_ops.json`](../../test/logic_ops.json) | Covered |
| NOT A | [`test/logic_ops.json`](../../test/logic_ops.json) | Covered |
| NOT B | [`test/logic_ops.json`](../../test/logic_ops.json) | Covered |
