tmarhguy/cpu/schematics/kicad/modules/gates/gate_and/gate_and_2in/gate_and_2in.kicad_pcb

## KiCad design schematics/kicad/modules/gates/gate_and/gate_and_2in/gate_and_2in.kicad_pcb (2026-01-07)

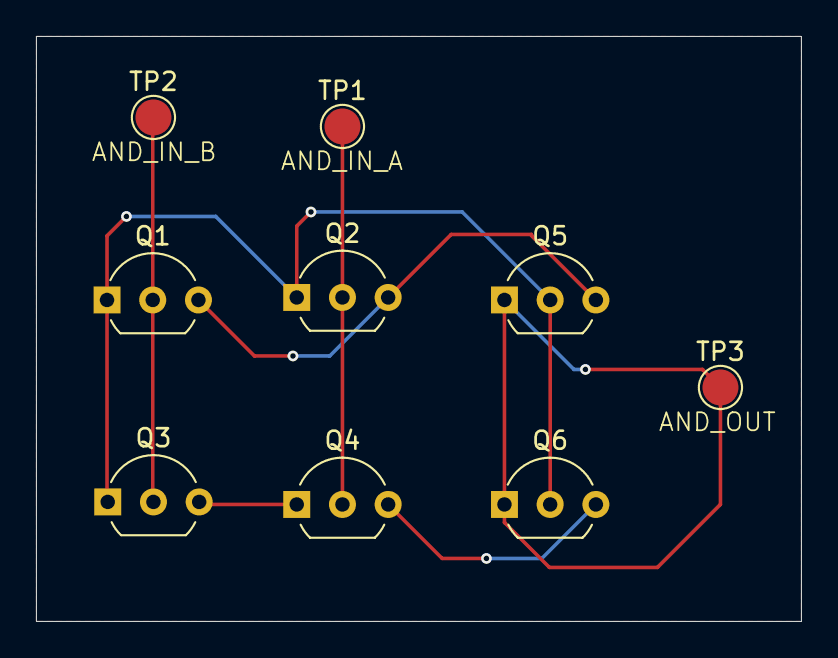
[picture p96: board gate_and_2in.kicad_pcb from above]

Board: 2 copper layers, 42.5 x 32.5 mm, 9 parts (0 on the bottom side), 7 nets.

Parts:
Q1, Q2, Q5: PMOS; TO-92_Inline_Wide
Q3, Q4, Q6: NMOS; TO-92_Inline_Wide
TP1: AND_IN_A; TestPoint_Pad_D2.0mm
TP2: AND_IN_B; TestPoint_Pad_D2.0mm
TP3: AND_OUT; TestPoint_Pad_D2.0mm

Connections:
/AND_IN_A: Q2.2 (G), Q4.2 (G), TP1.1
/AND_IN_B: Q1.2 (G), Q3.2 (G), TP2.1
/AND_OUT: Q5.1 (D), Q6.1 (D), TP3.1
GND: Q4.3 (S), Q6.3 (S)
unnamed: Q1.1 (D), Q2.1 (D), Q3.1 (D), Q5.2 (G), Q6.2 (G)
unnamed: Q3.3 (S), Q4.1 (D)
VCC: Q1.3 (S), Q2.3 (S), Q5.3 (S)
